DoctorWkt/2FISC/Docs/Figs/sp.png

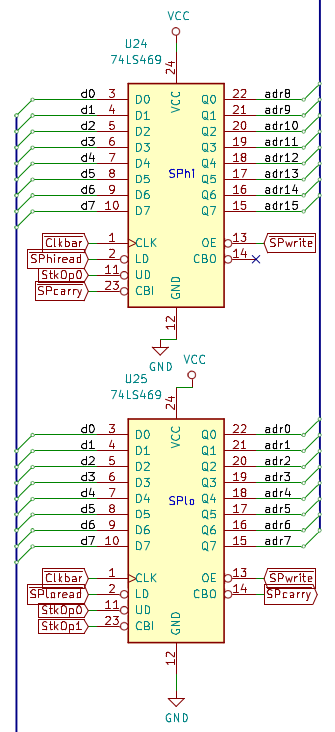
Docs/Figs/sp.png
