DoctorWkt/2FISC/Verilog/74238.v

// 3-line to 8-line decoder/demultiplexer (active high outputs)
// (c) Tim Rudy, GPL3

/* verilator lint_off DECLFILENAME */
module ttl_74238 #(parameter WIDTH_OUT = 8, WIDTH_IN = $clog2(WIDTH_OUT),
                   DELAY_RISE = 12, DELAY_FALL = 12)
(
  input Enable1_bar,
  input Enable2_bar,
  input Enable3,
  input [WIDTH_IN-1:0] A,
  output [WIDTH_OUT-1:0] Y
);

//------------------------------------------------//
reg [WIDTH_OUT-1:0] computed;
integer i;

always @(*)
begin
  for (i = 0; i < WIDTH_OUT; i++)
  begin
    if (!Enable1_bar && !Enable2_bar && Enable3 && i == A)
      computed[i] = 1'b1;
    else
      computed[i] = 1'b0;
  end
end
//------------------------------------------------//

assign #(DELAY_RISE, DELAY_FALL) Y = computed;

endmodule
